yvoronkin/FailDeadly/firmware/Inc/fd_log.h

#ifndef FD_LOG_H
#define FD_LOG_H

#define LOG_BUFFER_LEN  128
#define LOG_SEND_MAX_WAIT 100

void FDLogTaskInit(void);
int32_t FDSendLog(const unsigned char * buf, size_t len, int omit_rtos, int noblock);
void FDLogFreeRTOSStateInit(void);

#endif
